NaBo04/Lidar2D-prediction-on-prosthetic-legs/Entregables/PPT - Reu 2 Contraparte.pdf

## Integración de Percepción Geométrica Basada en LIDAR 2D para Anticipación de Terreno en Prótesis Transfemoral Activa

Grupo 2

IEE3112 - Proyecto de Título

## Diseño de soporte

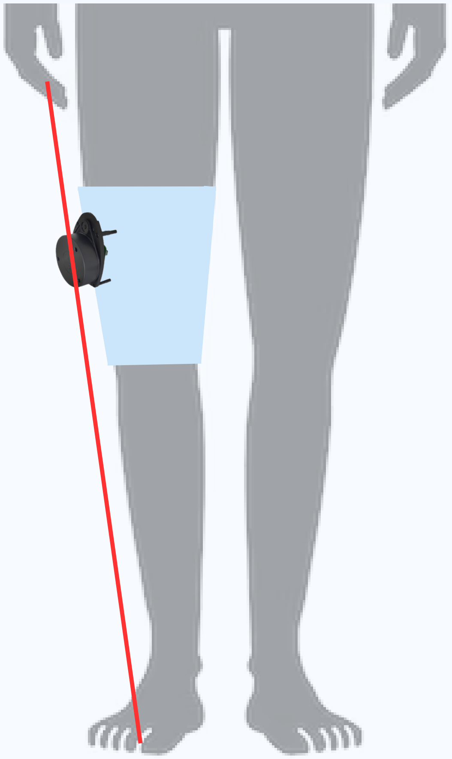
[picture p50: figure]

Si se usa un soporte plano, la pendiente natural del musculo orienta el sensor de manera incorrecta.

No apunta al suelo, apunta al pie.
Realizar un escaneo
inclinado.

## Diseño de soporte

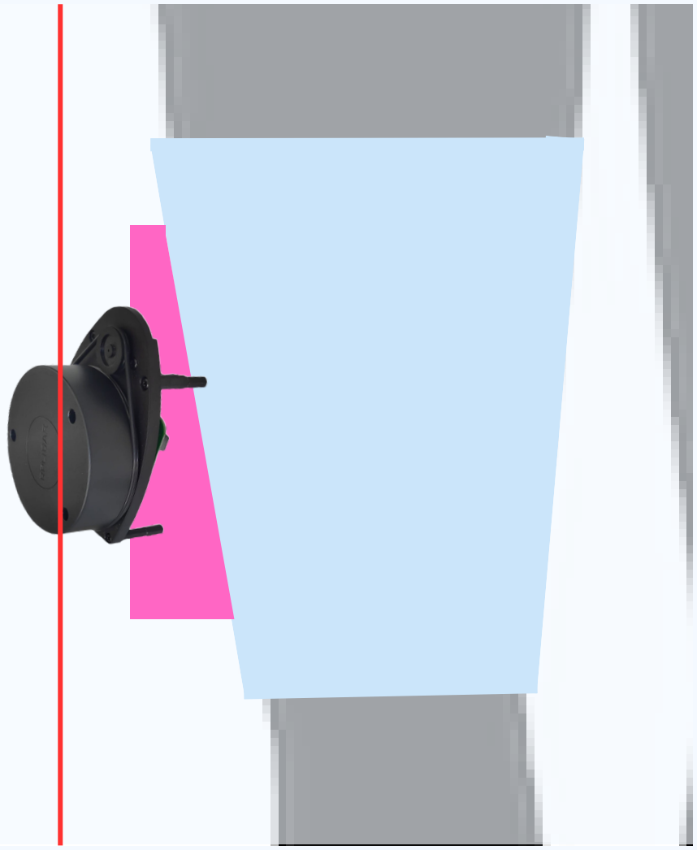
[picture p51: figure]

Al inclinar el soporte en 5,64° se permite corregir el error.

Sirve para ambas piernas

## Diseño de soporte

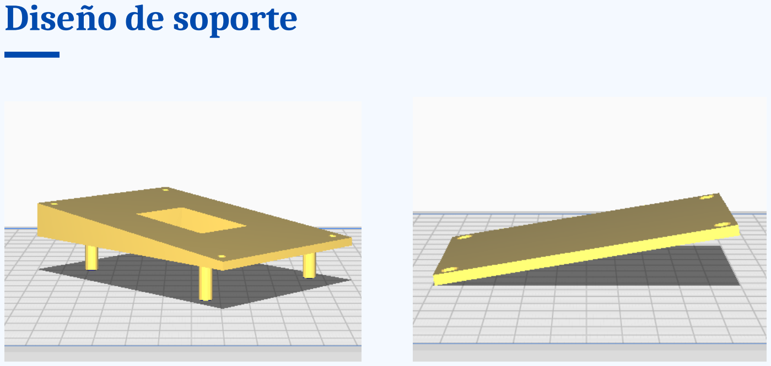
[picture p52: page 4]

## Controlador PWM Velocidad Motor DC 90W

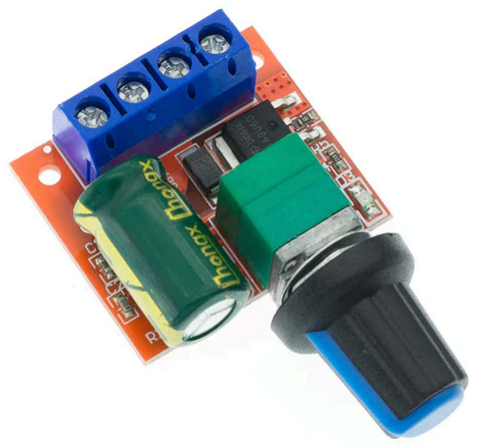
[picture p53: figure]

Módulo PWM de presición con dutycycle controlable mediante potenciómetro

Frecuencia PWM: 20kHz
Voltaje de funcionamiento: 4.5V – 35V DC Corriente de salida: 0 – 5A

## Pruebas con pesos

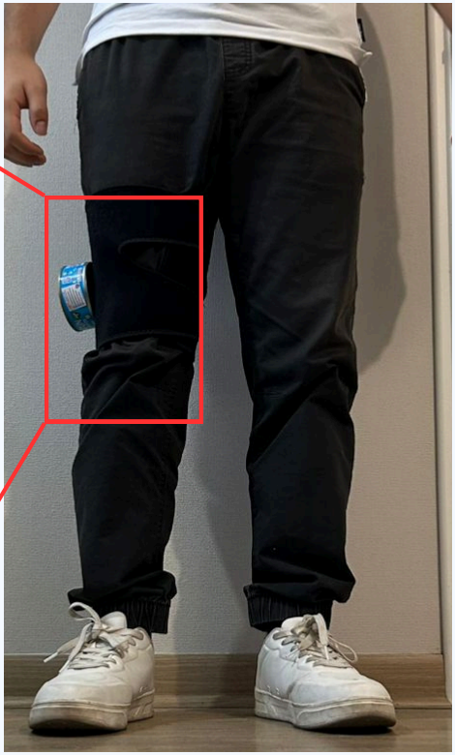
[picture p54: figure]
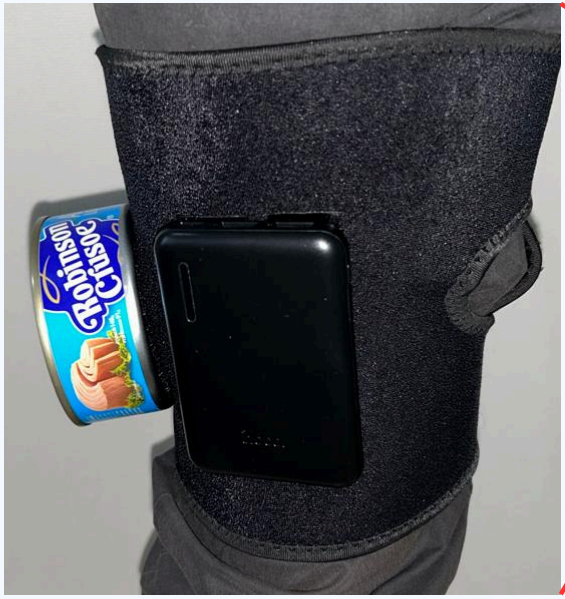
[picture p55: figure]

El sistema del LiDAR pesa
aprox. 150 g., usamos una lata de 140 g para simular el peso.

Realizamos pruebas en los 5 escenarios y se concluyo lo siguiente:
No se despega el peso
con el velcro.
No es incomodo para
moverse

## Diagrama bajo nivel del flujo de información

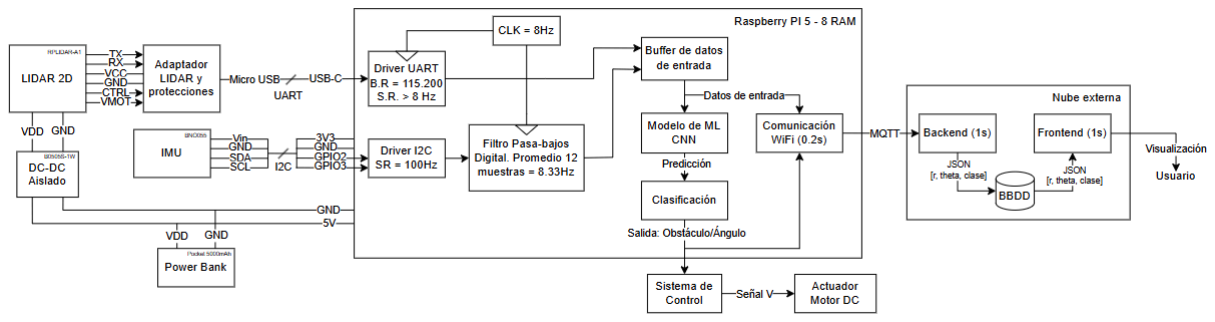
[picture p56: figure]

## Diagrama bajo nivel del flujo de información

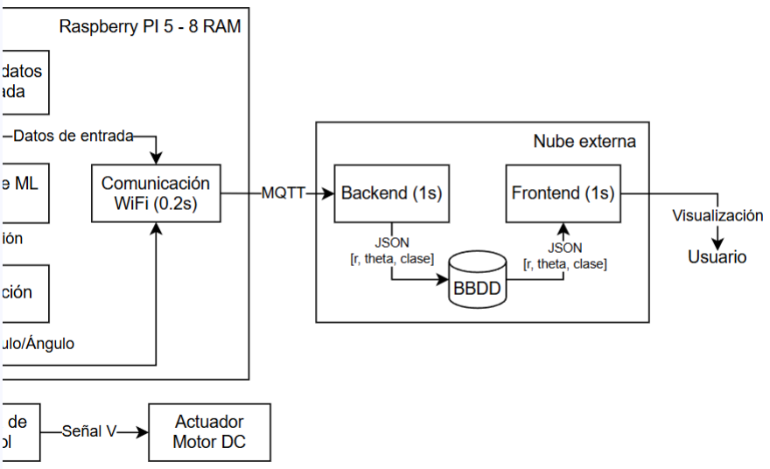
[picture p57: figure]

## Inicialización de la Raspberry

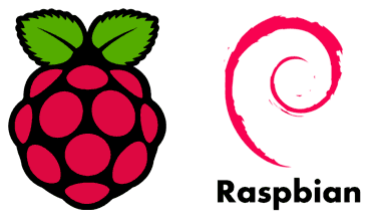
[picture p58: figure]
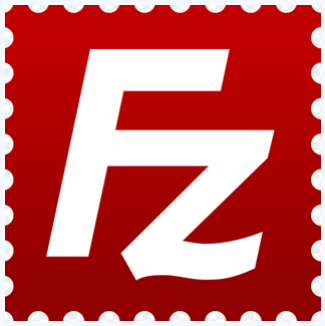
[picture p59: figure]

Se cargó Raspbian en la tarjeta de SD para generar la imagen
Se activó el SSH local y “global” usando Tailscale para manejo de IP El traspaso de diferentes archivos se hace a través de Filezilla
Esto permite un trabajo asíncrono desde cualquier lugar sin depender del hardware

## Bases de datos Lidar

Se buscaron distintas bases de datos relacionada a mediciones del Lidar, dentro de lo cual se presentan las siguientes desventajas
La mayoría de los datos están hechos en entornos Outdoor para UAV o pelotones
Gran mayoría de las bases de datos son en 3D Bases de datos 2D en Indoor tienen registros horizontales para mapear un camino para autos robóticos
En visión de Protesís no hay bases de datos públicas que usen Lidar 2D

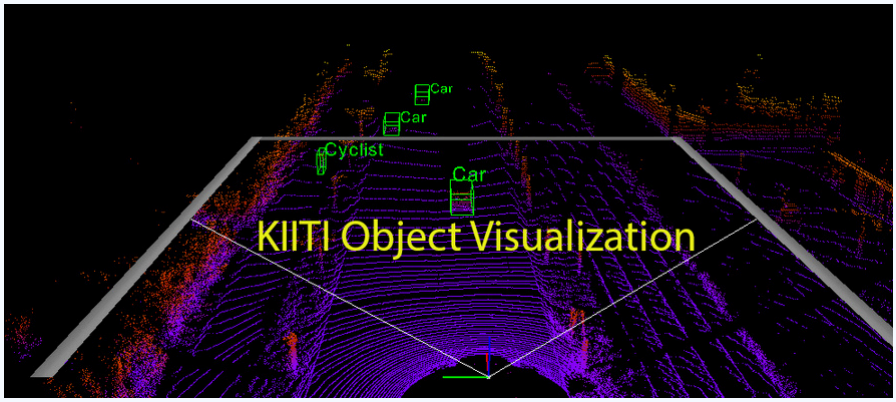
[picture p60: figure]

https://mindkosh.com/resources/autonomous-vehicles-lidar-datasets.html?ref=blog_

lookingoutforthehumansinaidataannotation

## Generación de datos sintéticos Lidar

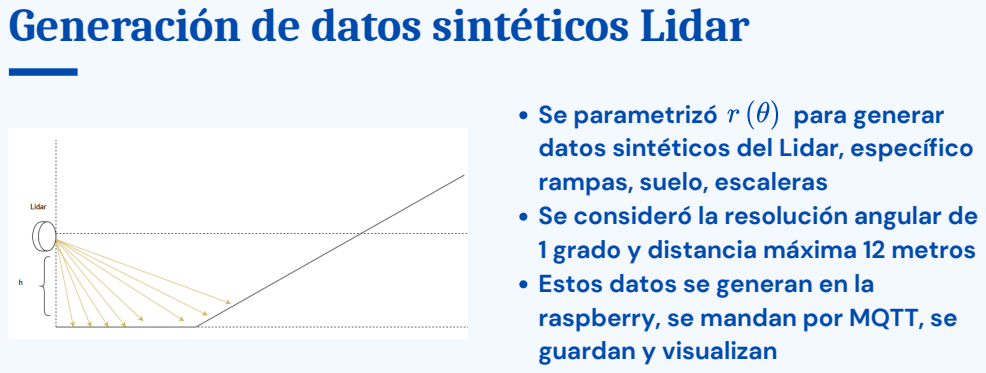
[picture p61: page 11]
Se parametrizó; para generar

datos sintéticos del Lidar, específico
rampas, suelo, escaleras
Se consideró la resolución angular de
1 grado y distancia máxima 12 metros
Estos datos se generan en la
raspberry, se mandan por MQTT, se
guardan y visualizan

## Protocolo de comunicación MQTT

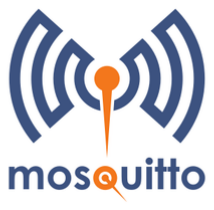
[picture p62: figure]

Se implementó MQTT con mosquitto el cual funciona sobre TCP para enviar datos a todos los computadores que esten subscritos a un topic “lidar/data”
Raspberry en este caso funciona como como publisher y host (broker)

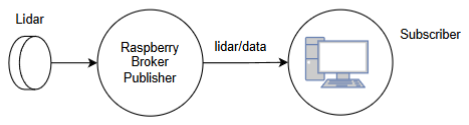
[picture p63: figure]

## Servicio de BDD

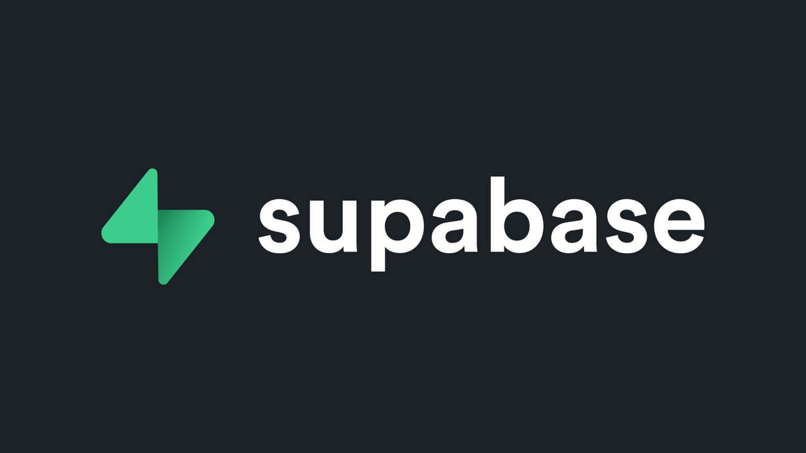
[picture p64: figure]

Se eligió supabase como servicio para almacenar los datos en línea. A continuación se enumeran las razones:

Implementación simple
Basada en PostgreSQL
Lectura y escritura en tiempo real Plan gratuito suficiente para los requerimientos del proyecto

## Estructura de la base de datos

La estructura de la base de datos actualmente tiene solo una tabla, donde guarda cada clasificación que recibe desde la raspberry, a continuación se muestra un ejemplo de esta

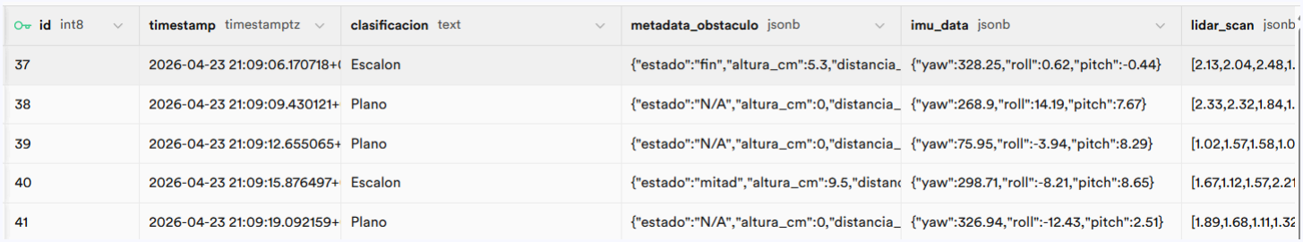
[picture p65: figure]

## Integración de Percepción Geométrica Basada en LIDAR 2D para Anticipación de Terreno en Prótesis Transfemoral Activa

Grupo 2

IEE3112 - Proyecto de Título
