NaBo04/Lidar2D-prediction-on-prosthetic-legs/Entregables/PPT - Reu 4 Contraparte.pdf

## Integración de Percepción Geométrica Basada en LIDAR 2D para Anticipación de Terreno en Prótesis Transfemoral Activa

Grupo 2

IEE3112 - Proyecto de Título

## Toma de muestras

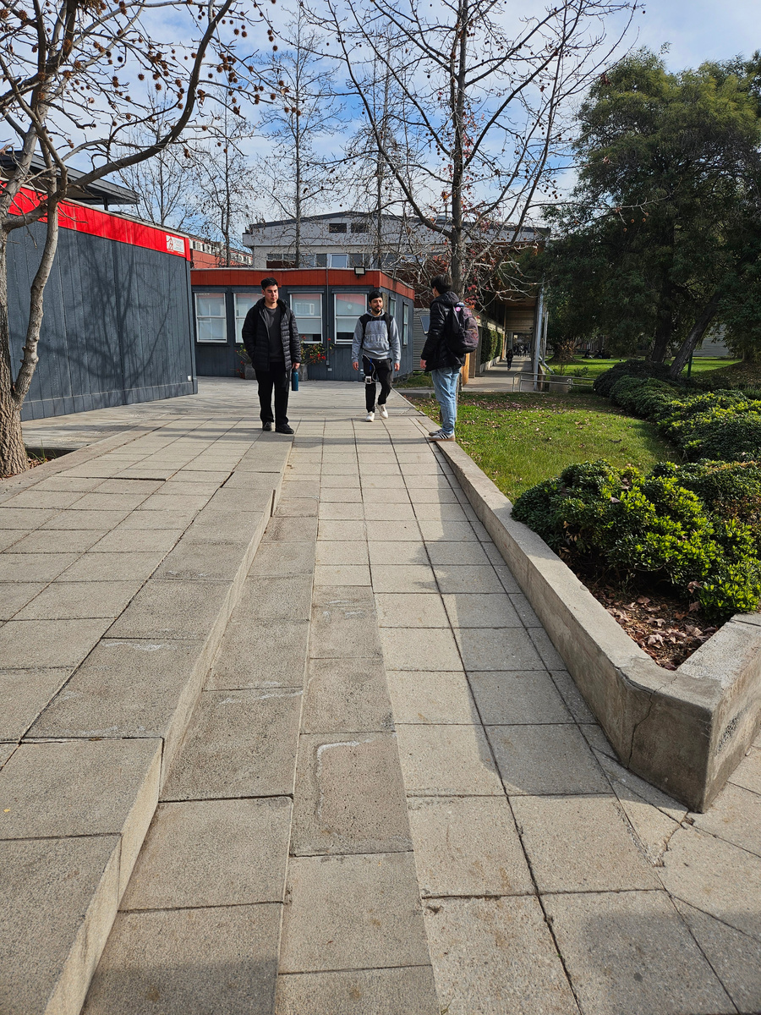
[picture p66: figure]

Tomamos una cantidad total de 2.630 muestras.

Probamos en diferentes entornos dentro de la universidad de noche.

Repetimos el mismo procedimiento de toma de muestras para cada entorno.

## Toma de muestras

Procedimiento de toma de muestras: Suelos

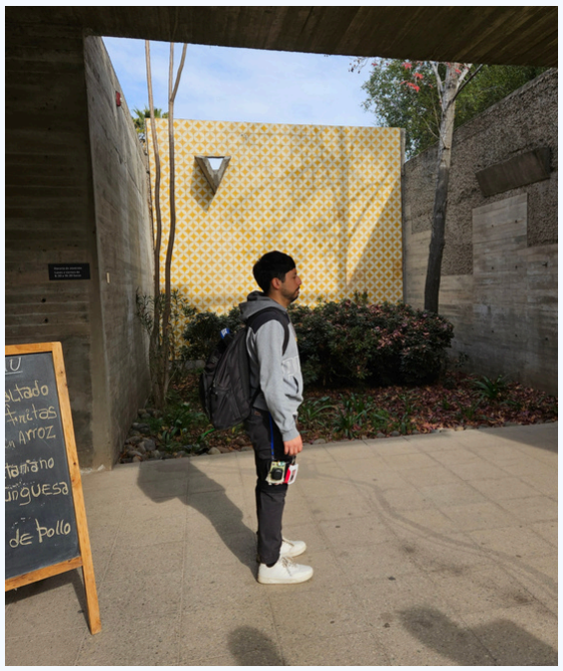
[picture p67: figure]
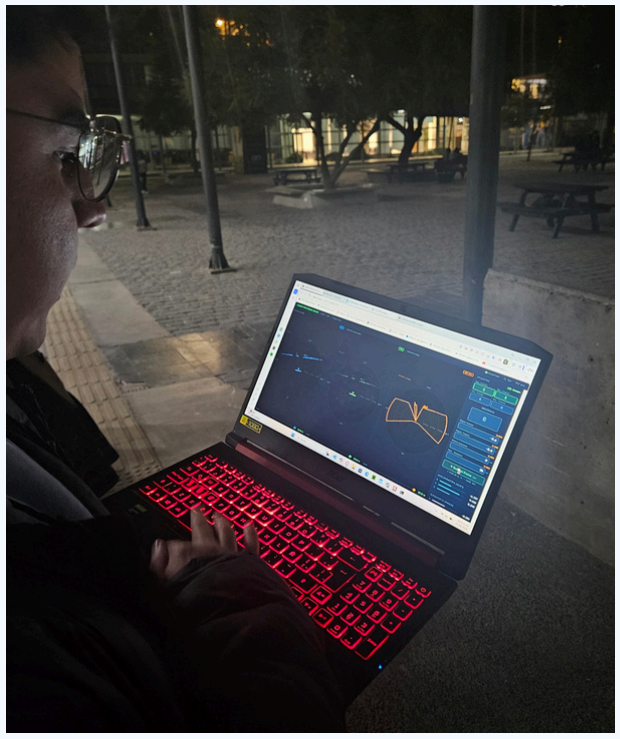
[picture p68: figure]

## Toma de muestras

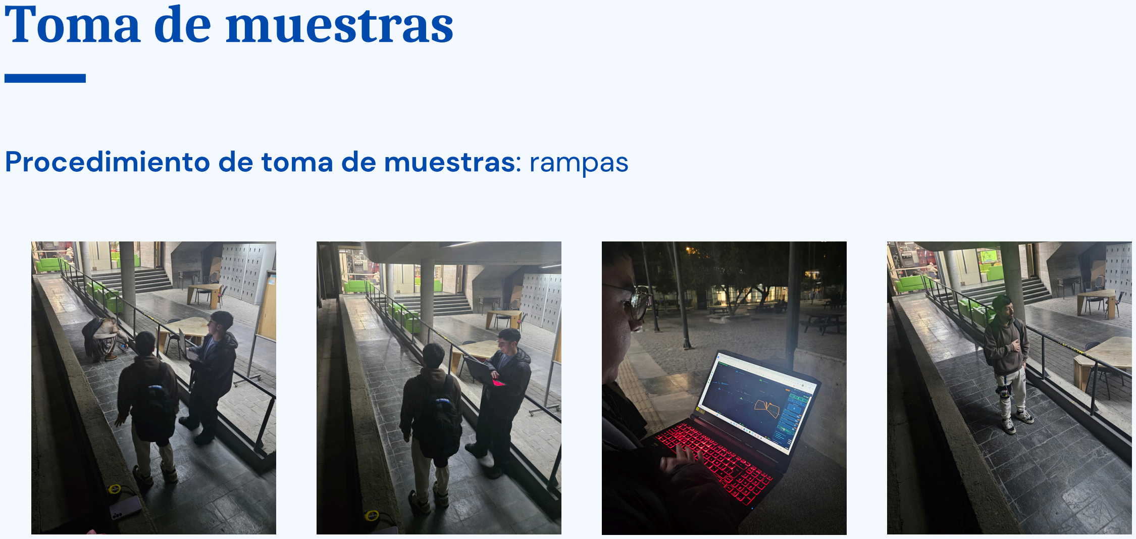
[picture p69: page 4]

Procedimiento de toma de muestras: rampas

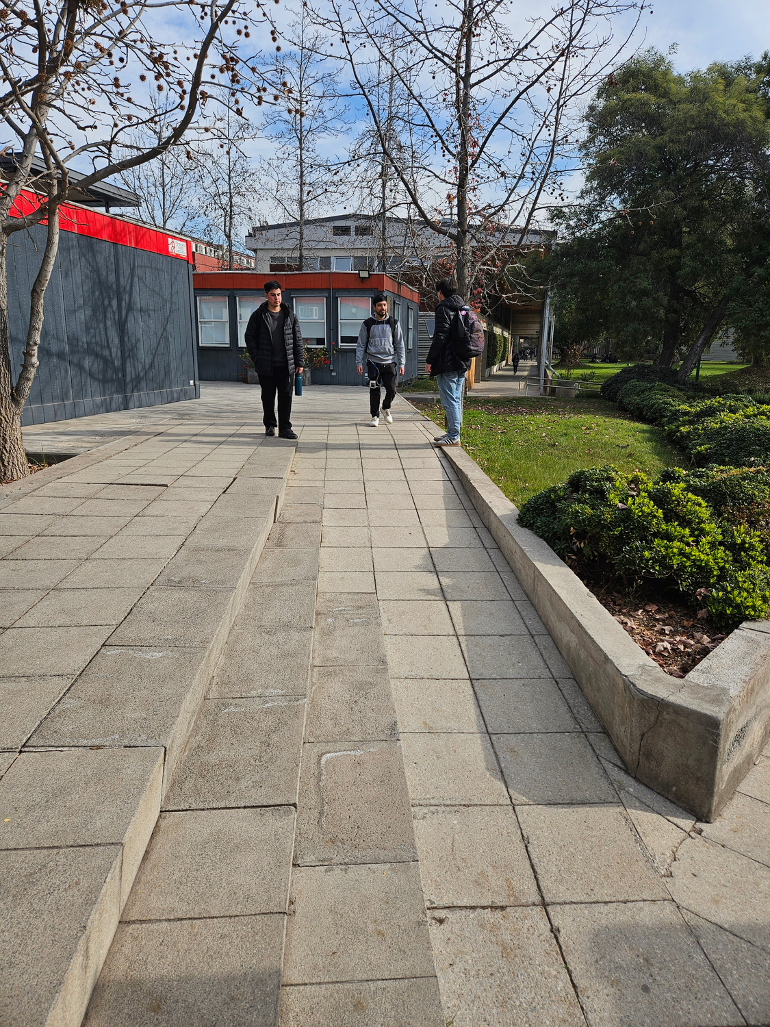
[picture p70: figure]

## Toma de muestras

Procedimiento de toma de muestras: Escaleras y obstaculos

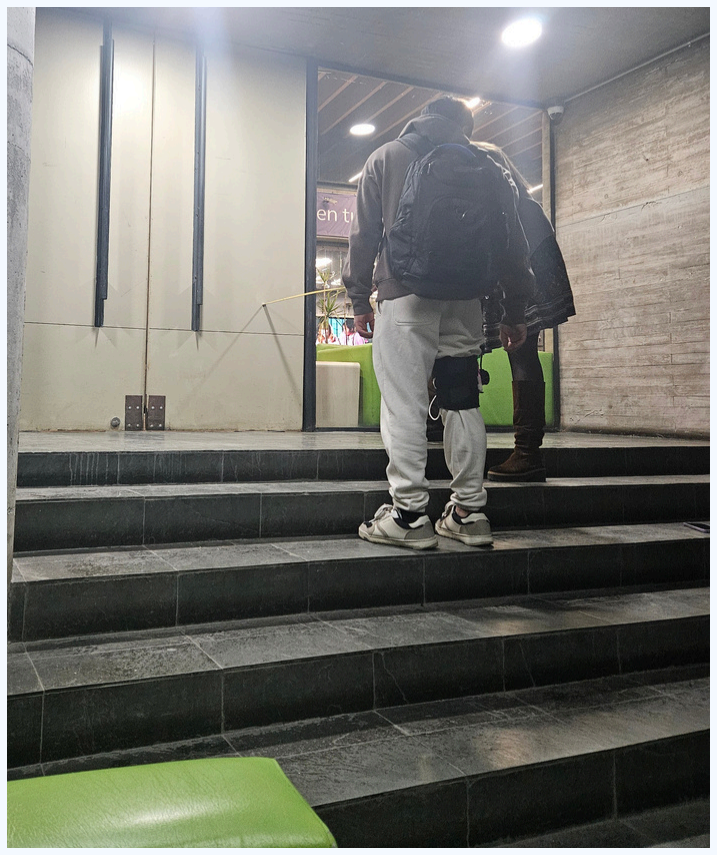
[picture p71: figure]
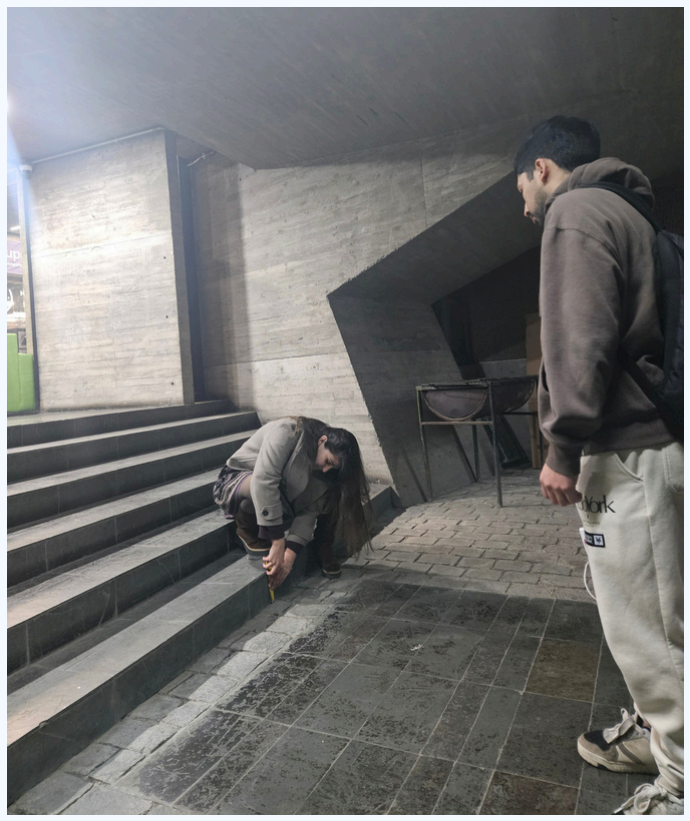
[picture p72: figure]

## PCB

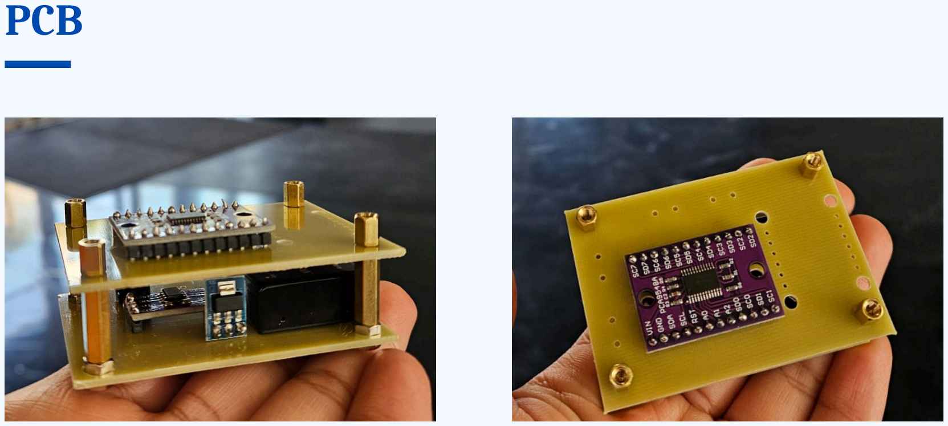
[picture p73: page 7]
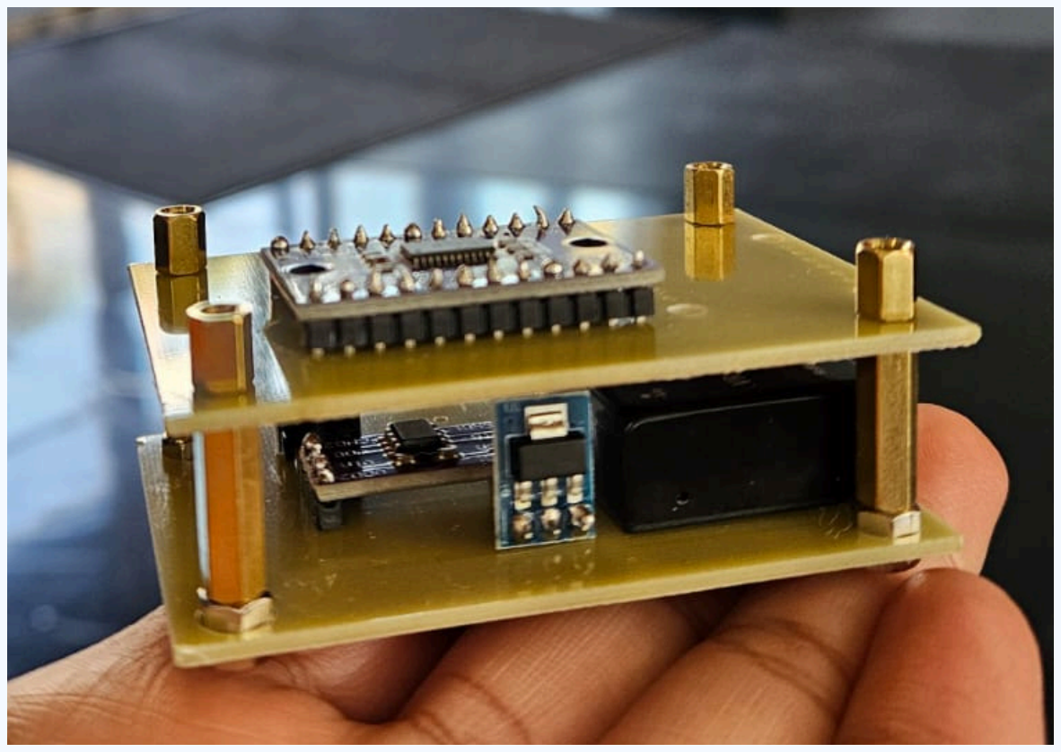
[picture p74: page 8]

## PCB

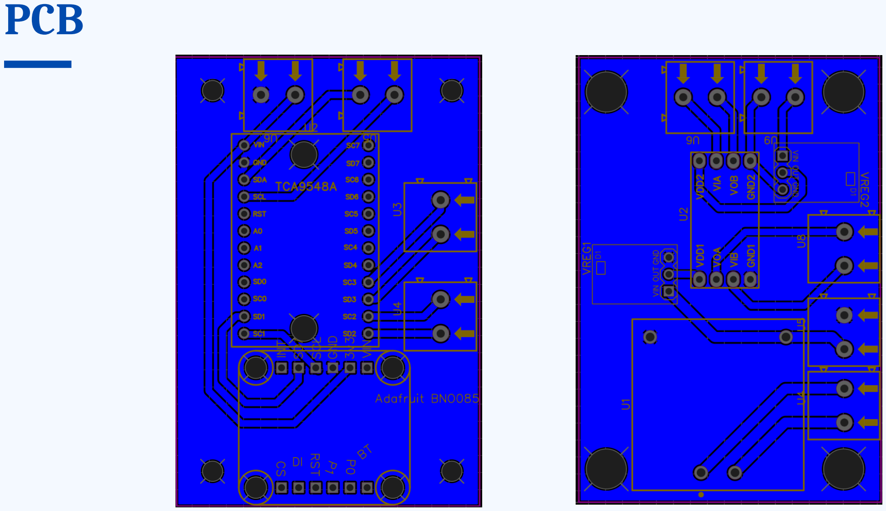
[picture p75: page 9]

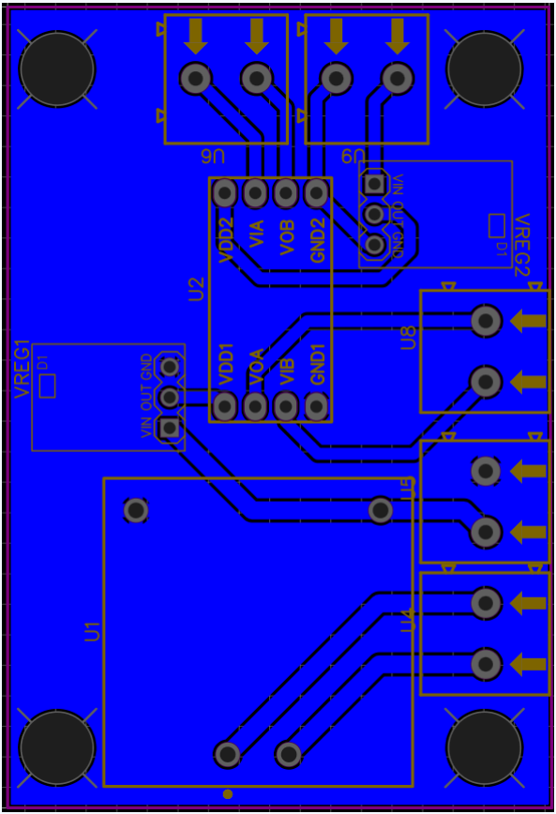
[picture p76: figure]

## Soporte para prótesis

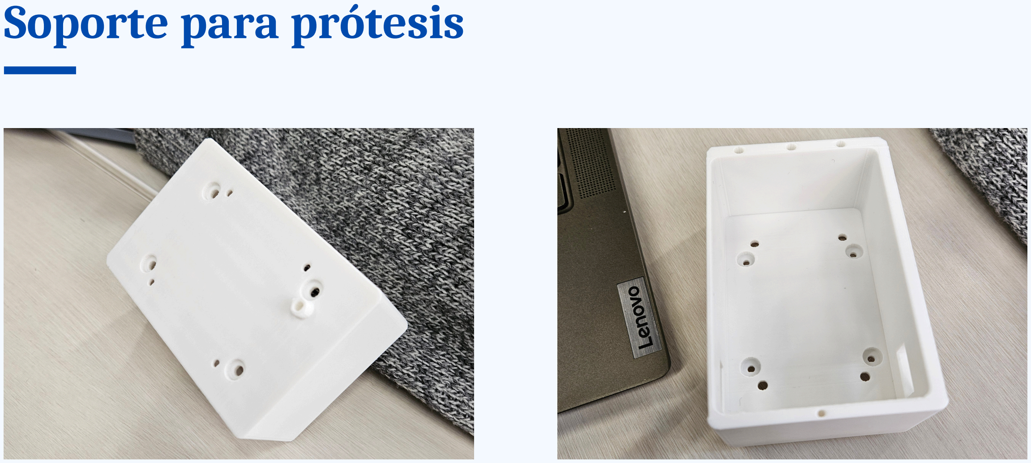
[picture p77: page 11]

## Soporte para prótesis

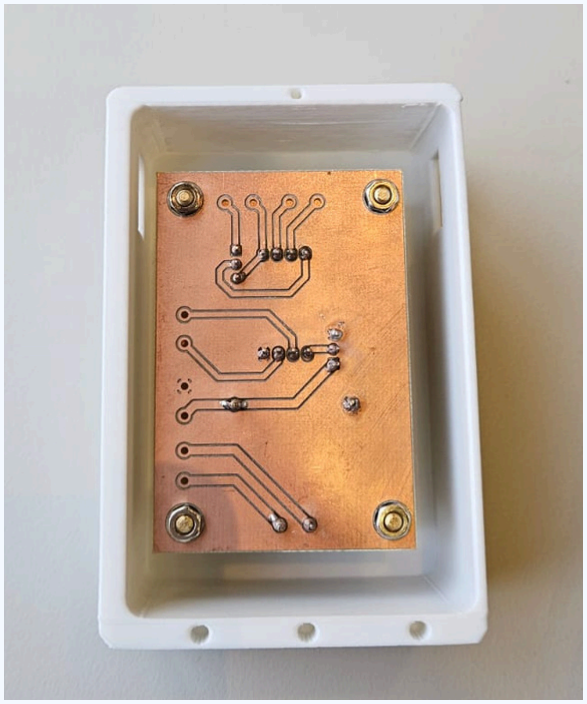
[picture p78: figure]
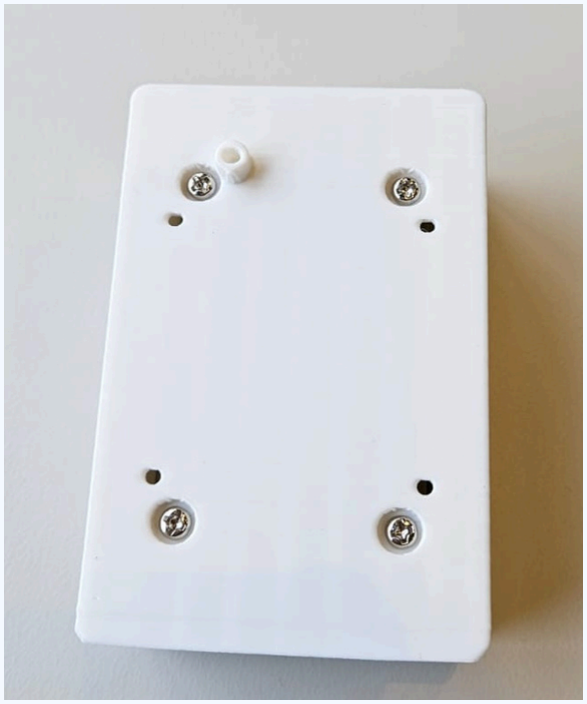
[picture p79: figure]

## Soporte para prótesis

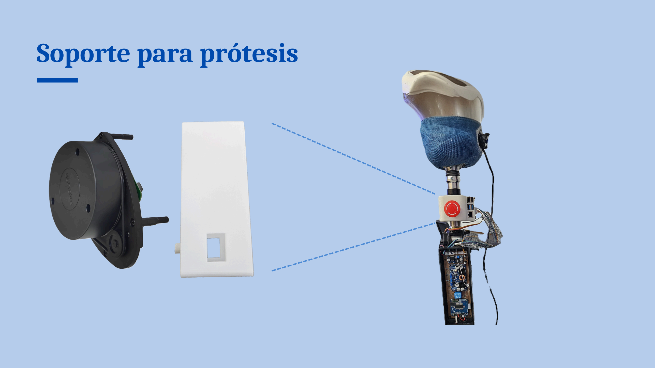
[picture p80: page 13]

## Topología red usada - red Tipo 1

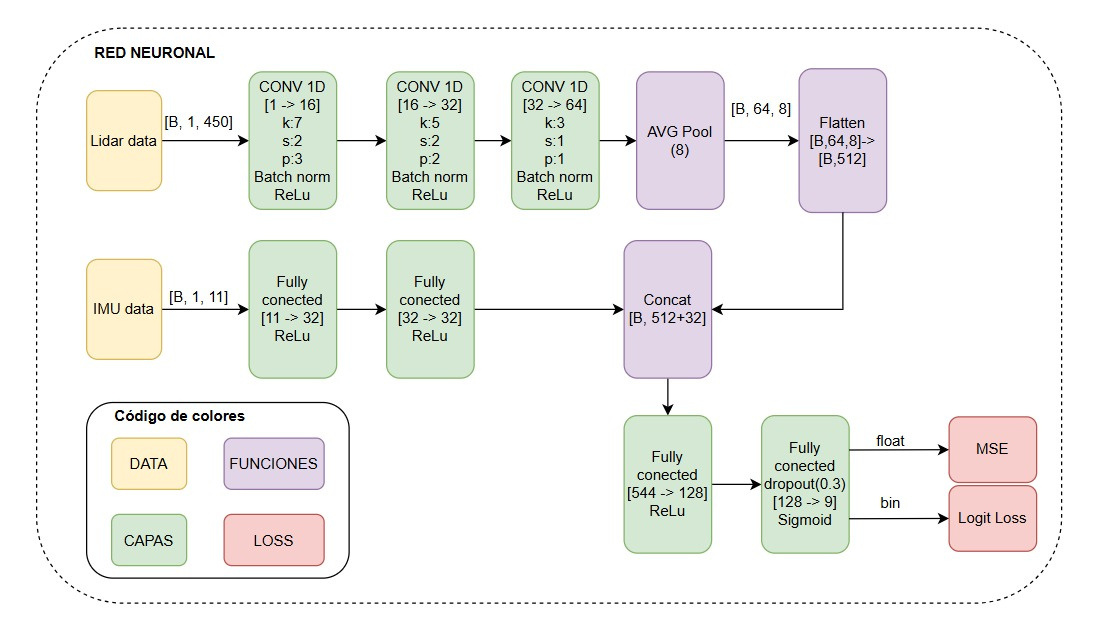
[picture p81: figure]

## Topología red usada - red Tipo 2

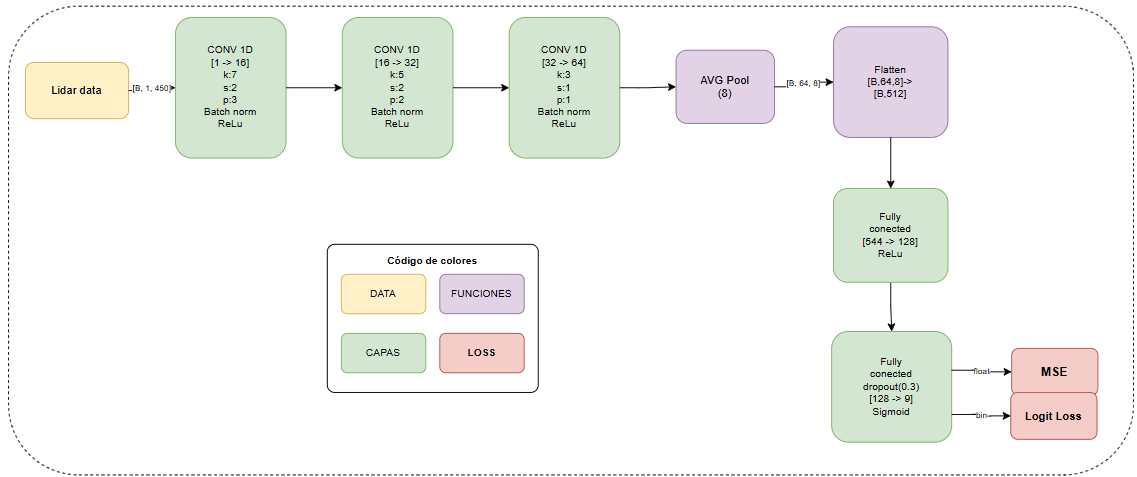
[picture p82: figure]

Metrica/Red | Loss | Val Loss | Val Acc
Lidar interpolado +IMU | 0.048 | 0.0167 | 99.73%
Lidar interpolado | 0.024 | 0.0247 | 99.74%
Distacia y ángulo reales Lidar | Trabajo futuro | Trabajo futuro | Trabajo futuro

## Resultados de entrenamiento

## Limitaciones - inferencias desde raspberry

Funciona bien para entornos abiertos

En entornos cerrados los obstáculo los reconoce como escalera.

En rampa hay error de 1.5 grados.

En obstáculos hay 20 cm de error en distancias lejanas, a distancia cercana 3 cm de error.

# Prueba en vivo

## Pasos a seguir

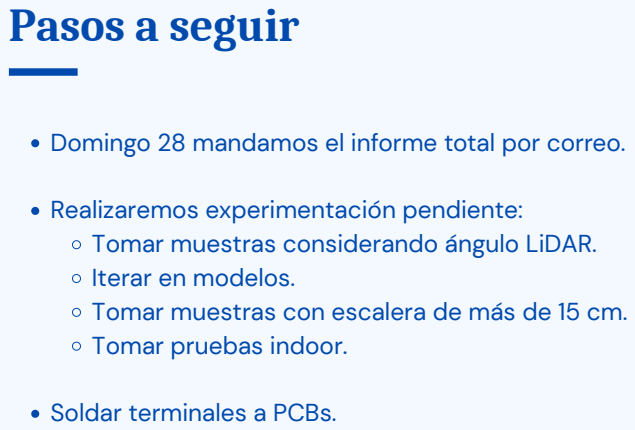
[picture p83: page 19]

Domingo 28 mandamos el informe total por correo.

Realizaremos experimentación pendiente:
Tomar muestras considerando ángulo LiDAR.
Iterar en modelos.
Tomar muestras con escalera de más de 15 cm.
Tomar pruebas indoor.

Soldar terminales a PCBs.

## Pasos a seguir

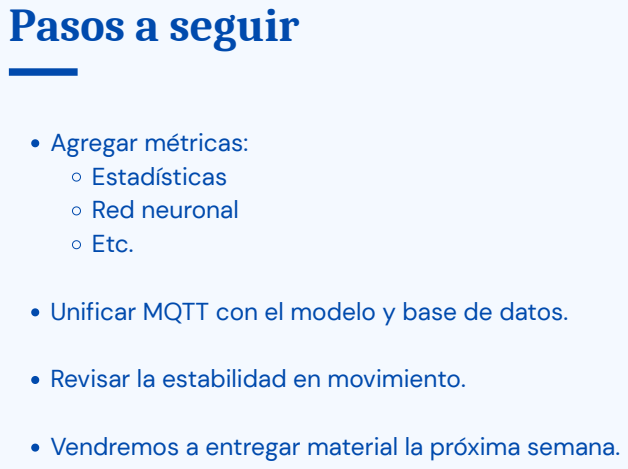
[picture p84: page 20]
Agregar métricas: Estadísticas Red neuronal Etc.

Unificar MQTT con el modelo y base de datos.

Revisar la estabilidad en movimiento.

Vendremos a entregar material la próxima semana.

## Integración de Percepción Geométrica Basada en LIDAR 2D para Anticipación de Terreno en Prótesis Transfemoral Activa

Grupo 2

IEE3112 - Proyecto de Título
