NaBo04/Lidar2D-prediction-on-prosthetic-legs/Entregables/PPT - Reu 5 Contraparte.pdf

Integración de Percepción
Geométrica Basada en LIDAR 2D para Anticipación de
Terreno en Prótesis
Transfemoral Activa

Grupo 2

IEE3112 - Proyecto de Título

Base de Datos - Muestras LIDAR

Distancia entre ángulos: 0.8°
Cantidad de datos por muestra: 450 Relleno de datos vacios: -1
Método de estandarización: Interpolación

Base de Datos - 1 Muestra

Datos LIDAR: [theta1, theta2, tehta3, ...]

Tiempo

450 total

### 2 Dimensiones

Datos IMU: [GSCP

_

x, GSCP

_y, GSCP

_

z, ...]

Bases de Datos

Tiempo

Datos
Solo 1 muestra

### 5 muestras

### 20 muestras

Solo LIDAR

LIDAR
estabilizado

LIDAR + IMU
sin estabilizar

Vector 1D
1x450

Matriz 2D
1x5x450

Matriz 2D
1x20x450

Vector 1D
1x450

Matriz 2D
1x5x450

Matriz 2D
1x20x450

Matriz 2D
1x2x450

Matriz 3D
1x2x5x450

Matriz 3D
1x2x20x450

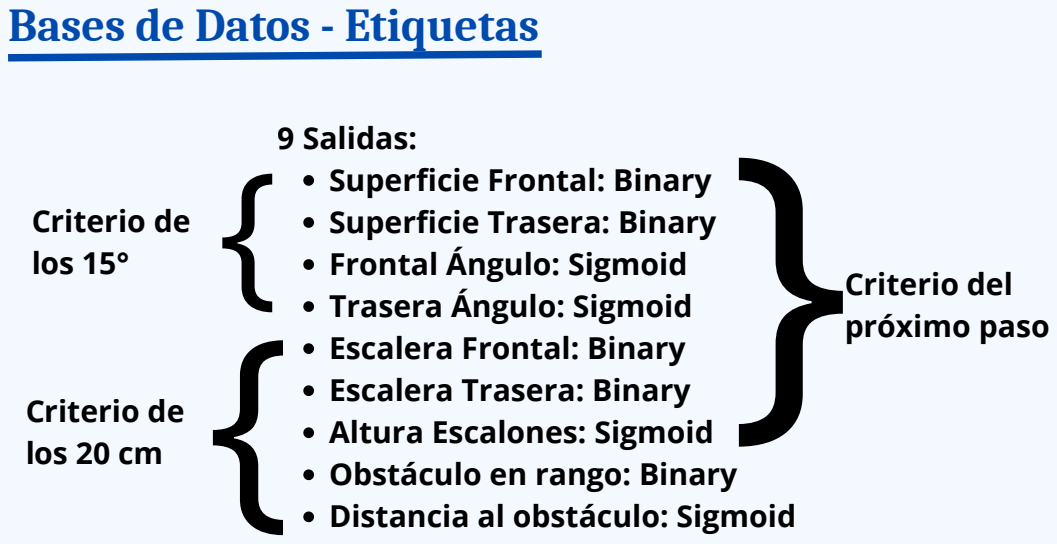
[picture p85: page 5]
Criterio del }; próximo paso; Criterio de los 20 cm; Criterio de los 15°

Bases de Datos - Etiquetas

9 Salidas:
Superficie Frontal: Binary
Superficie Trasera: Binary
Frontal Ángulo: Sigmoid
Trasera Ángulo: Sigmoid
Escalera Frontal: Binary
Escalera Trasera: Binary
Altura Escalones: Sigmoid
Obstáculo en rango: Binary
Distancia al obstáculo: Sigmoid

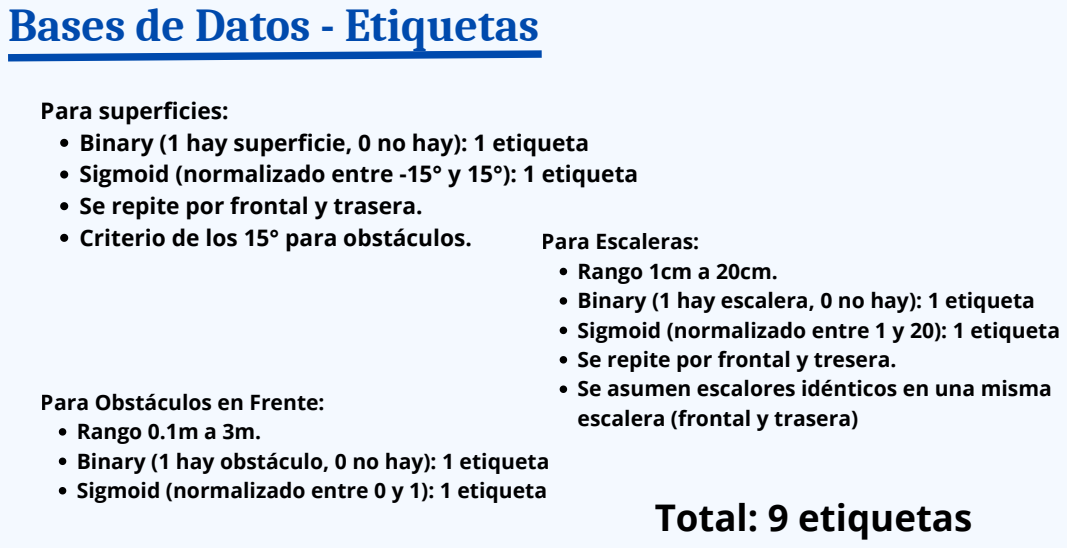
[picture p86: page 6]

Bases de Datos - Etiquetas

Para superficies:
Binary (1 hay superficie, 0 no hay): 1 etiqueta
Sigmoid (normalizado entre -15° y 15°): 1 etiqueta
Se repite por frontal y trasera.
Criterio de los 15° para obstáculos.

Para Escaleras:
Rango 1cm a 20cm.
Binary (1 hay escalera, 0 no hay): 1 etiqueta
Sigmoid (normalizado entre 1 y 20): 1 etiqueta
Se repite por frontal y tresera.
Se asumen escalores idénticos en una misma
escalera (frontal y trasera)
Total: 9 etiquetas

Para Obstáculos en Frente:
Rango 0.1m a 3m.
Binary (1 hay obstáculo, 0 no hay): 1 etiqueta
Sigmoid (normalizado entre 0 y 1): 1 etiqueta

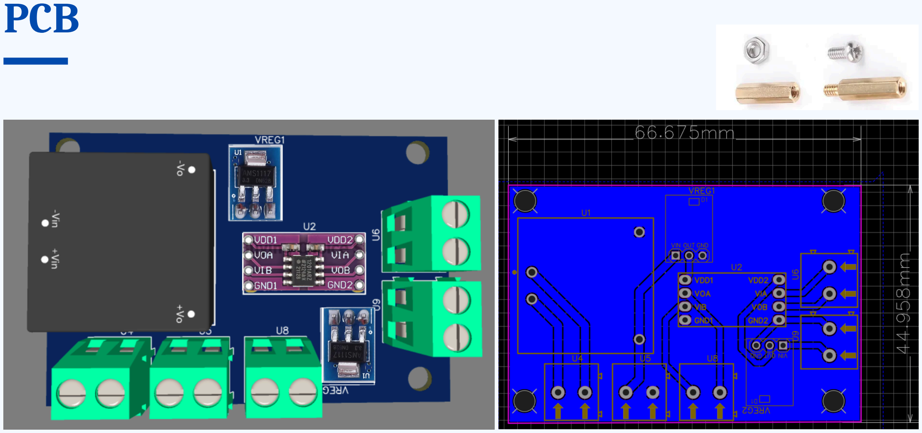
[picture p87: page 7]

PCB

Propuesta integración LiDAR a prótesis

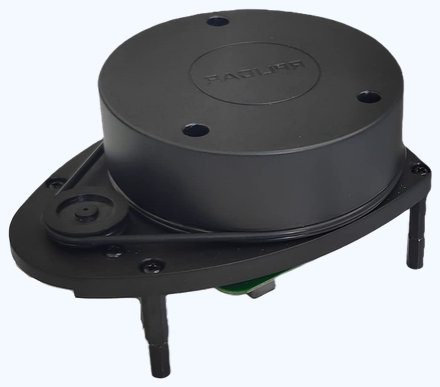
[picture p88: figure]
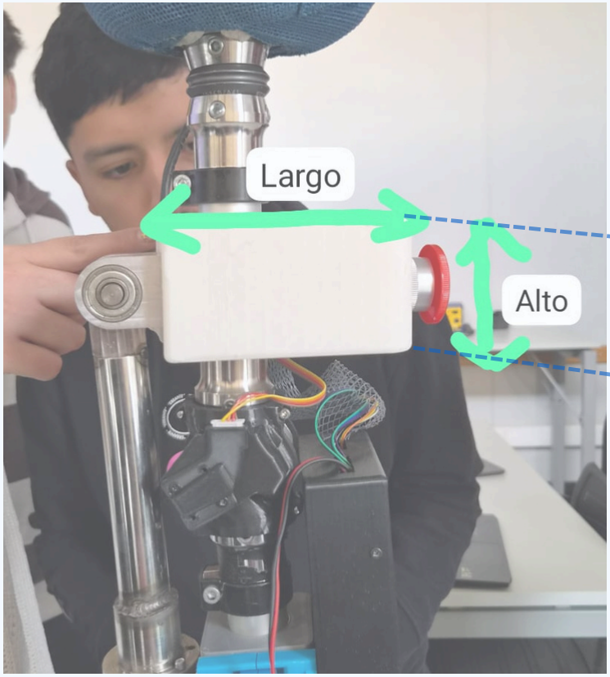
[picture p89: figure]
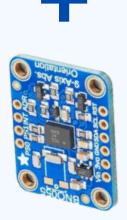
[picture p90: figure]

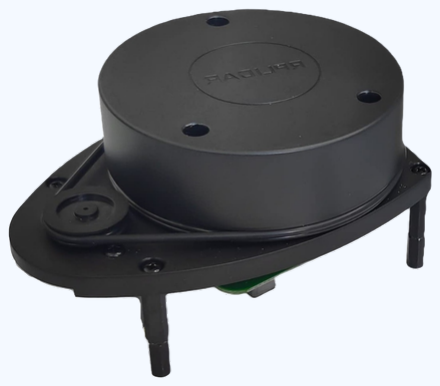
[picture p91: figure]
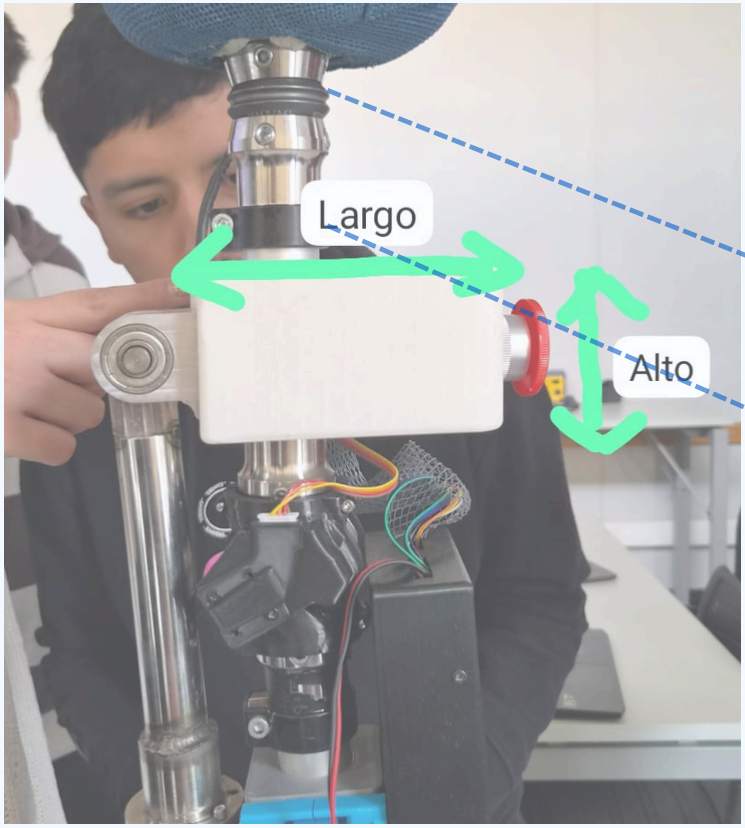
[picture p92: figure]

+

Propuesta integración LiDAR a prótesis

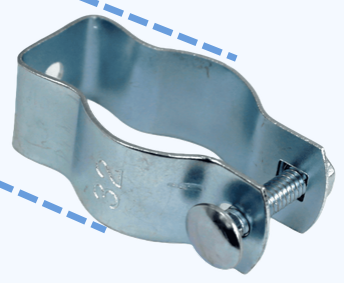
[picture p93: figure]
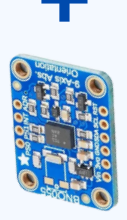
[picture p94: figure]

+

+

Preguntas

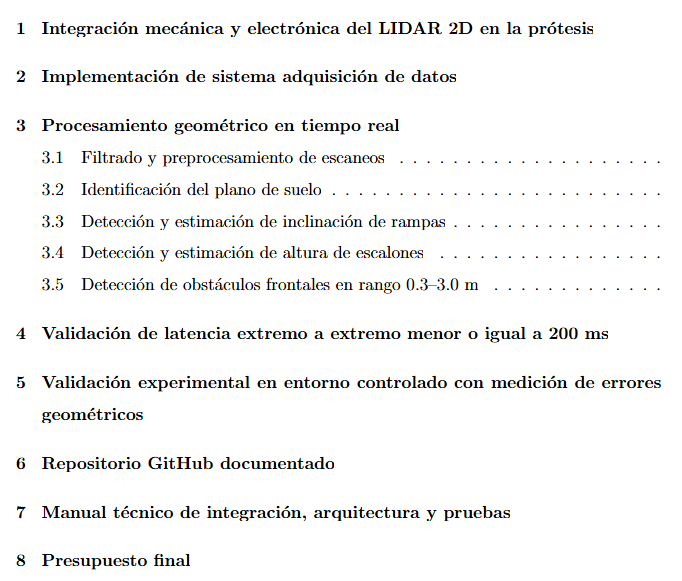
[picture p95: figure]

Formato entrega final:
¿Está bien un informe equivalente al Hito 1 con los aspectos solicitados para el Hito 2?

Integración de Percepción
Geométrica Basada en LIDAR 2D para Anticipación de
Terreno en Prótesis
Transfemoral Activa

Grupo 2

IEE3112 - Proyecto de Título
