NaBo04/Lidar2D-prediction-on-prosthetic-legs/Entregables/PPT- Reu 1 Contraparte.pdf

## Integración de Percepción Geométrica Basada en LIDAR 2D para Anticipación de Terreno en Prótesis Transfemoral Activa

Grupo 2

IEE3112 - Proyecto de Título

## Diagrama de bloques - Alto nivel

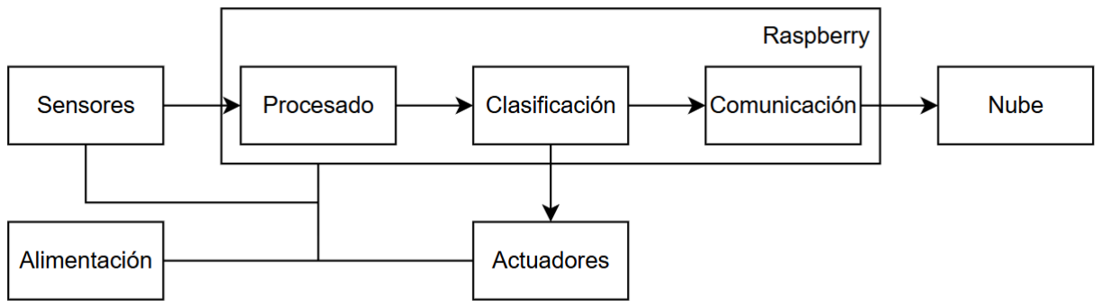
[picture p96: figure]

## Diagrama de bloques - Medio nivel

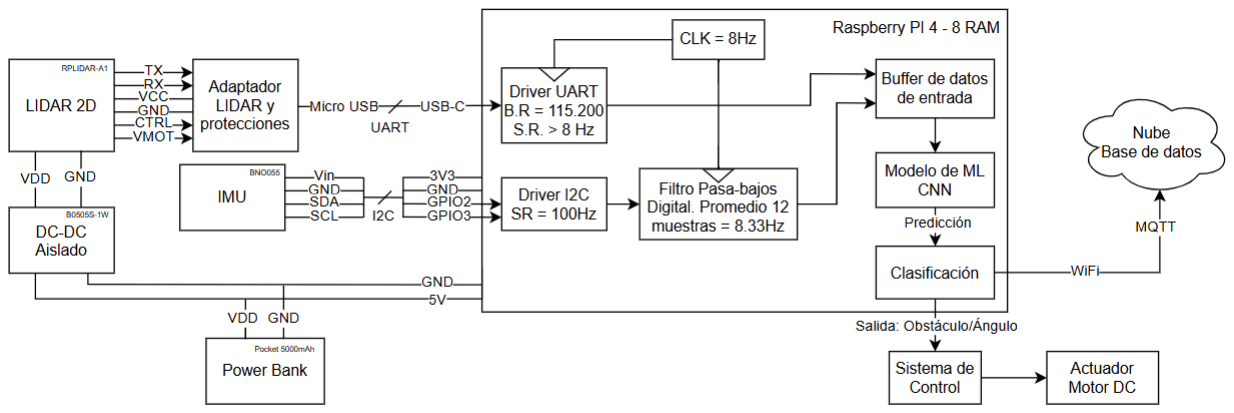
[picture p97: figure]

## Lidar - Alimentación

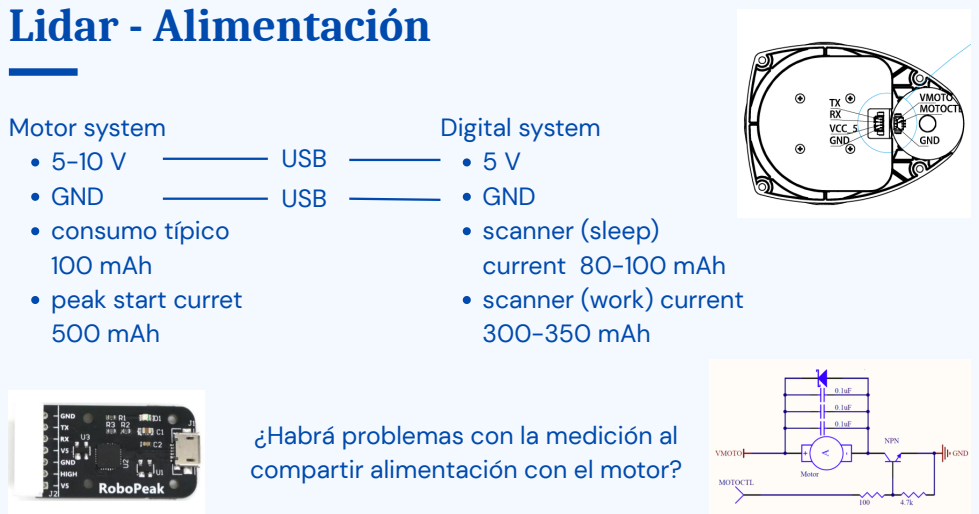
[picture p98: page 4]
Motor system 5-10 V GND consumo típico 100 mAh peak start curret 500 mAh; USB USB

Digital system
GND
scanner (sleep)
current 80-100 mAh
scanner (work) current
300-350 mAh

¿Habrá problemas con la medición al
compartir alimentación con el motor?

## LIDAR - Especificaciones

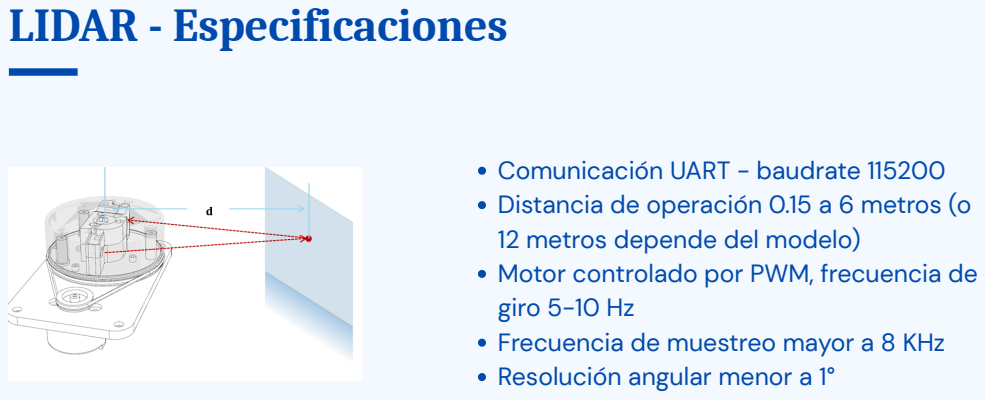
[picture p99: page 5]

Comunicación UART - baudrate 115200
Distancia de operación 0.15 a 6 metros (o
12 metros depende del modelo)
Motor controlado por PWM, frecuencia de
giro 5-10 Hz
Frecuencia de muestreo mayor a 8 KHz
Resolución angular menor a 1°

## Sensores adicionales

Se vió la necesidad de agregar un sensor IMU para compensar la inclinación de la pierna en las mediciones del LiDAR

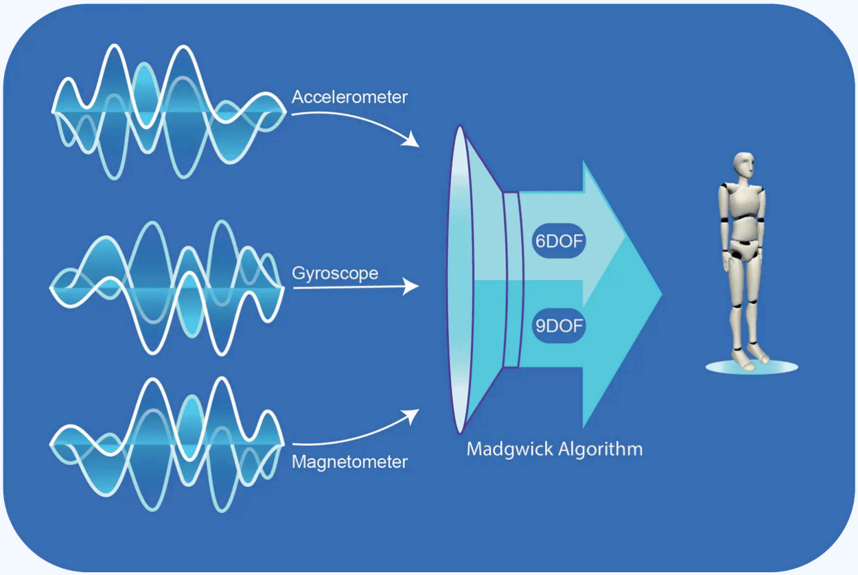
[picture p100: figure]

Fuente (https://qsense-motion.com/how-do-imu-motion-sensors-work/)

## IMU: BNO055

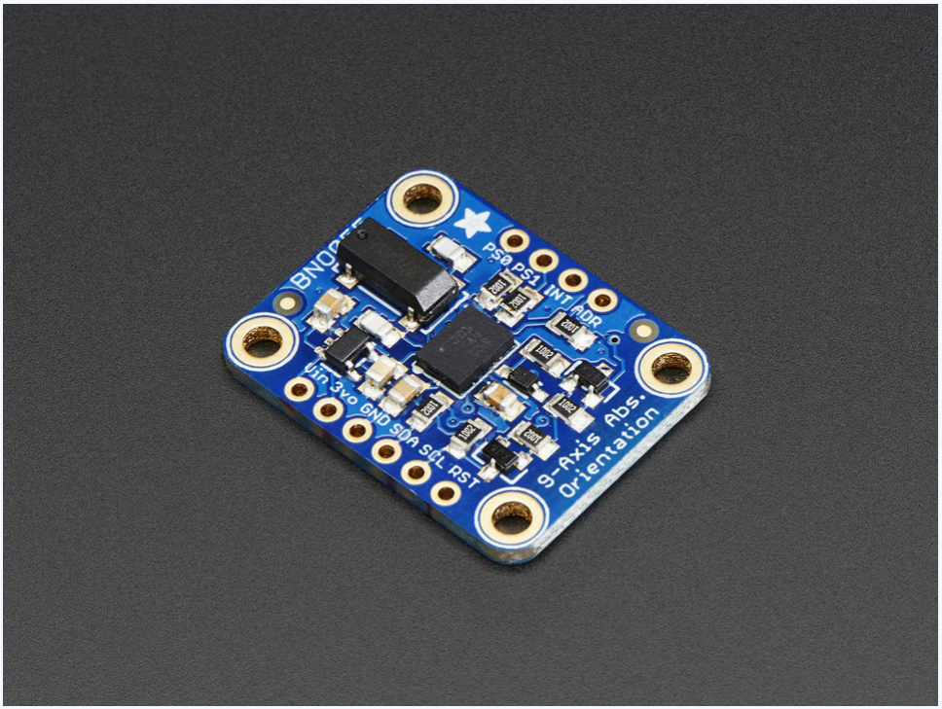
[picture p101: figure]

Se escogió el IMUBNO055 por la entrega directa de los ángulos euler o quaterniones, simplificando la implementación de un filtro de Kalman o Madgwick. Permitiendo enfocar esfuerzos en el LiDAR y la clasificación de obstáculos.

El breakout utilizado será el Adafruit 9-
DOF Absolute Orientation IMU Fusion Breakout

## IMU: BNO055

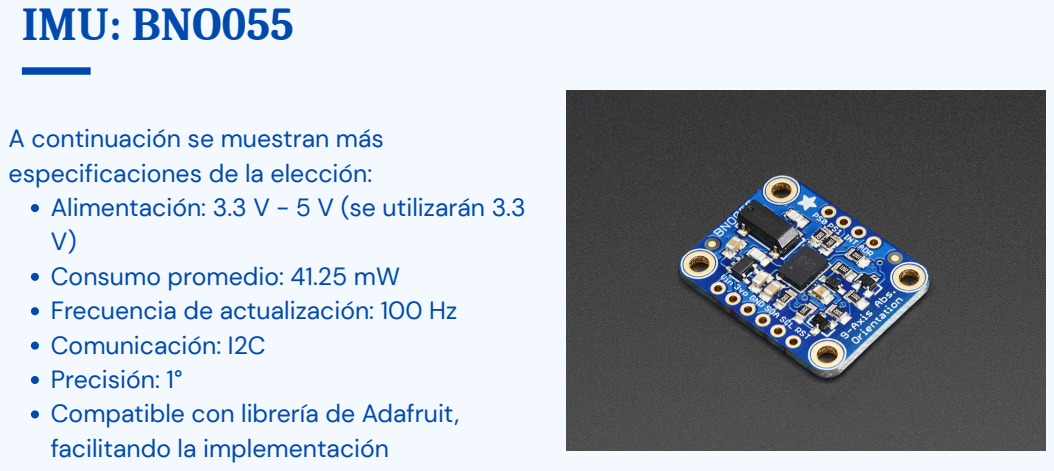
[picture p102: page 8]

A continuación se muestran más
especificaciones de la elección:
Alimentación: 3.3 V - 5 V (se utilizarán 3.3
Consumo promedio: 41.25 mW
Frecuencia de actualización: 100 Hz
Comunicación: I2C
Precisión: 1°
Compatible con librería de Adafruit,
facilitando la implementación

## Consumo

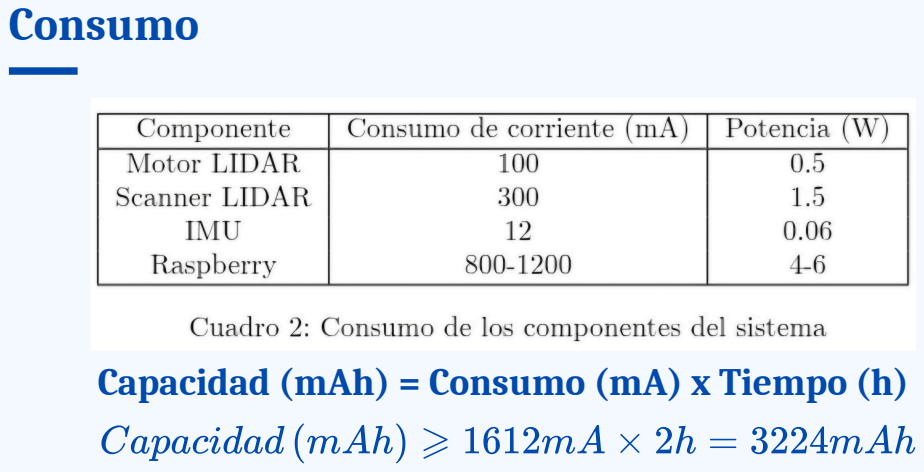
[picture p103: page 9]

Capacidad (mAh) = Consumo (mA) x Tiempo (h)

## Alimentación

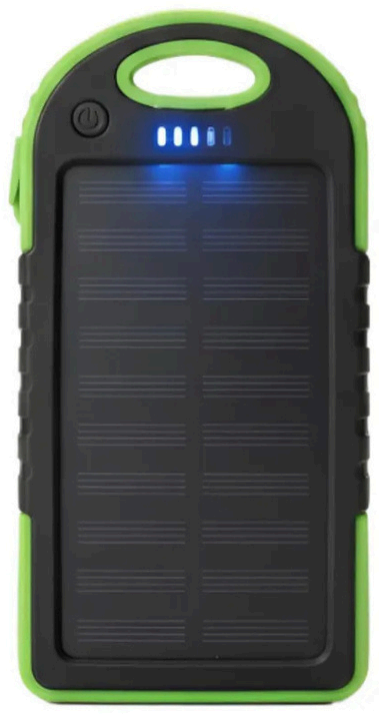
[picture p104: figure]

## Peso neto: 150g Dimensiones: 142x75x13.6 mm Panel solar: 1.2W Monocristalino Capacidad de baterías : 5000 mAh Voltaje: 5V DC

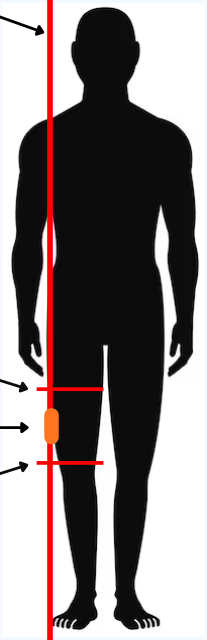
[picture p105: figure]
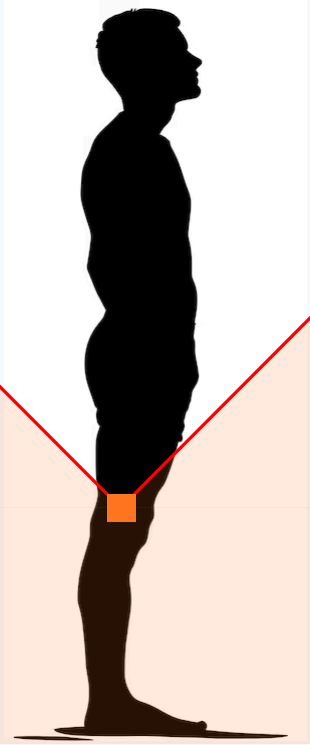
[picture p106: figure]

Plano de
observación

LIDAR 2D + IMU

## Disposición para Pruebas

Área de
observación
Rodilla

necesaria

Socket

## Soporte para Pruebas

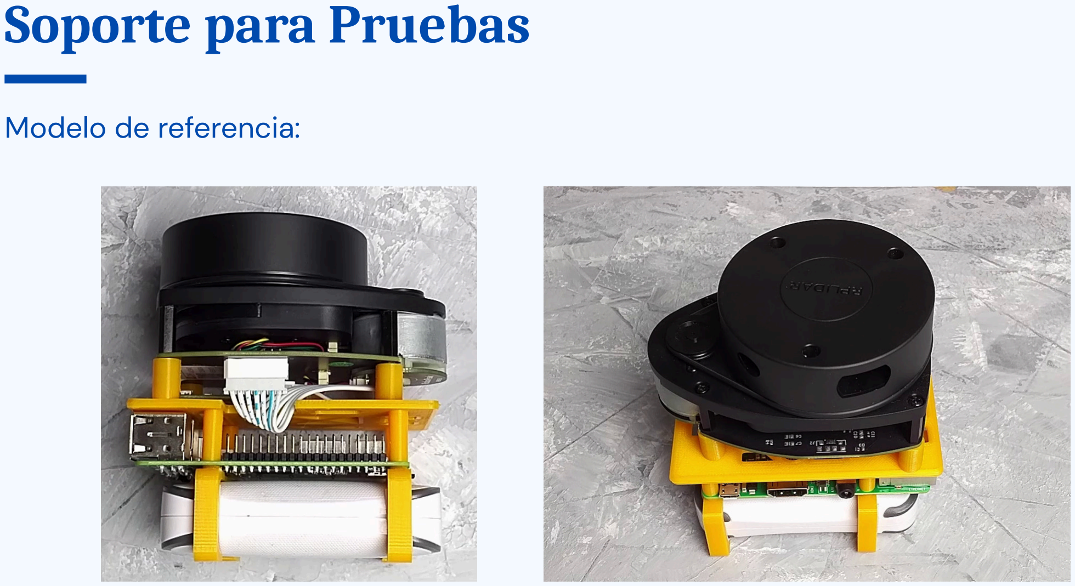
[picture p107: page 12]

Modelo de referencia:

## Soporte para Pruebas

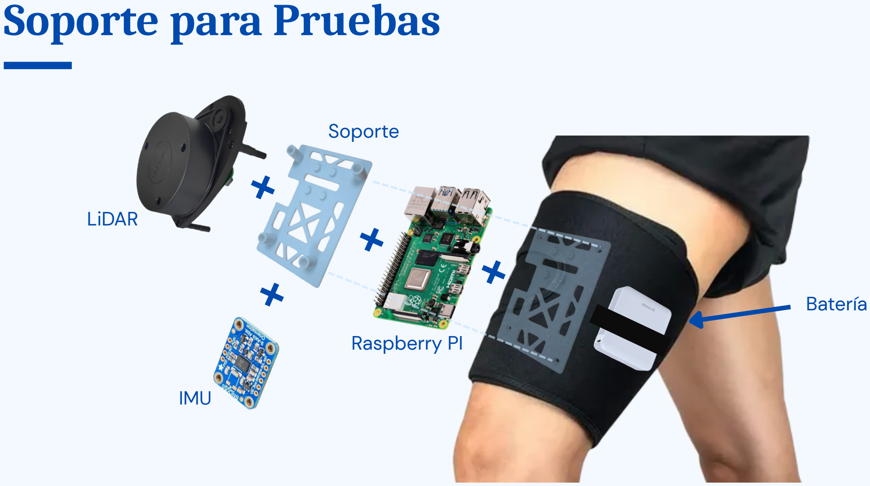
[picture p108: page 13]

+

+

+
+

IMU

Batería

LiDAR

Soporte

Raspberry PI

## Soporte para Pruebas

Otra idea de banda de compresión:

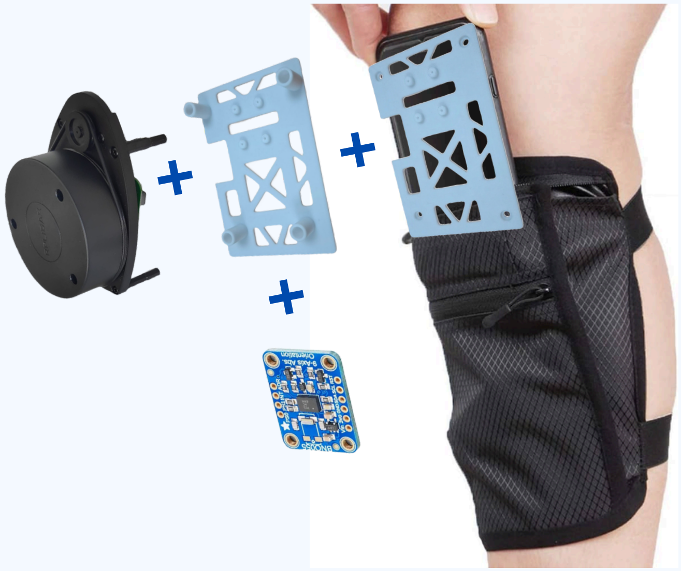
[picture p109: figure]
